LukasKropf/nadia-hardware/housing/Explosion.png

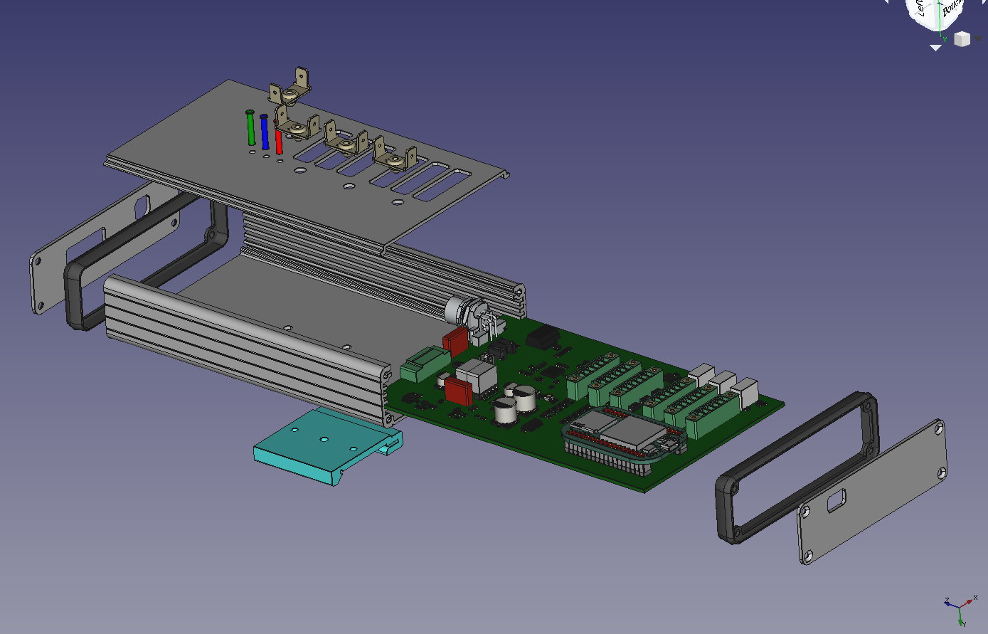
housing/Explosion.png
