LukasKropf/nadia-hardware/housing/Explosion_transparten_Beschriftet.png

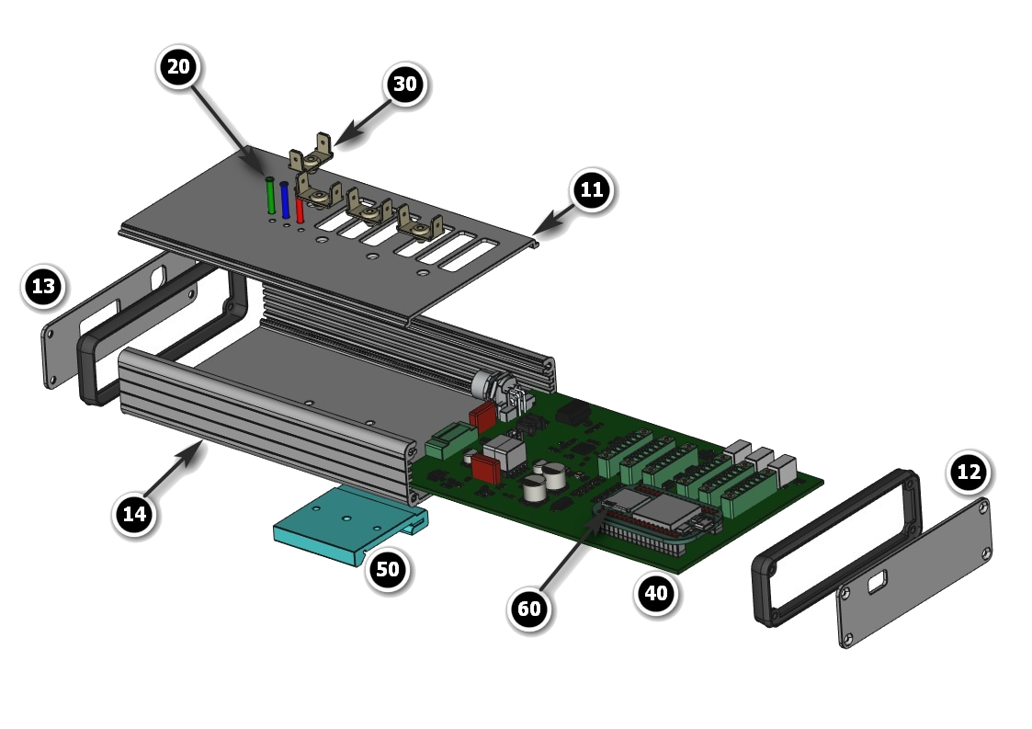
housing/Explosion_transparten_Beschriftet.png
