LukasKropf/nadia-hardware/housing/Explosion_weiss.jpg

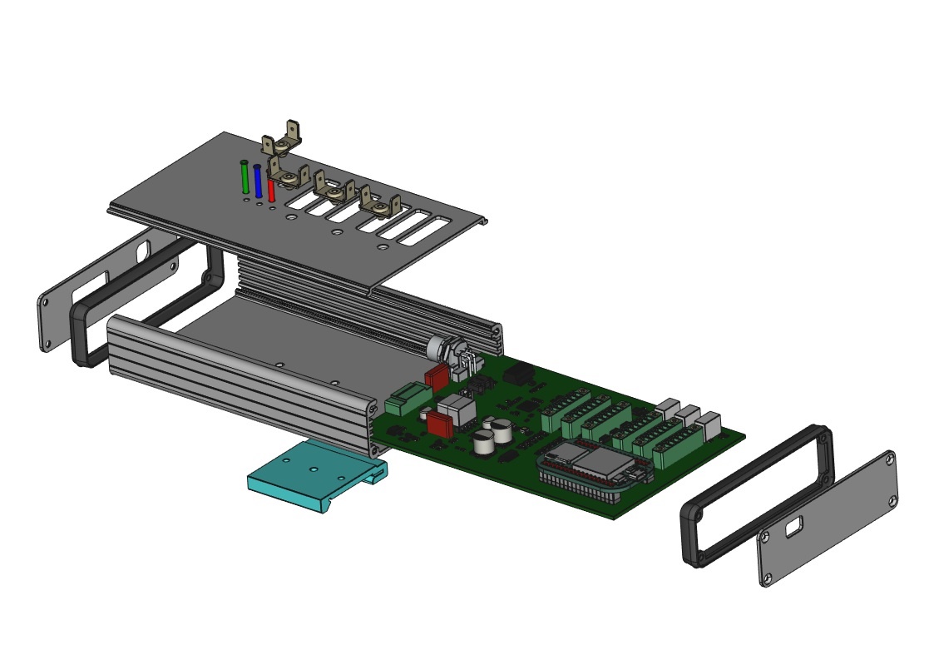
housing/Explosion_weiss.jpg
