LukasKropf/nadia-hardware/PCB/Simulationen/2018-10-04_212918_LUKAS-PC.png

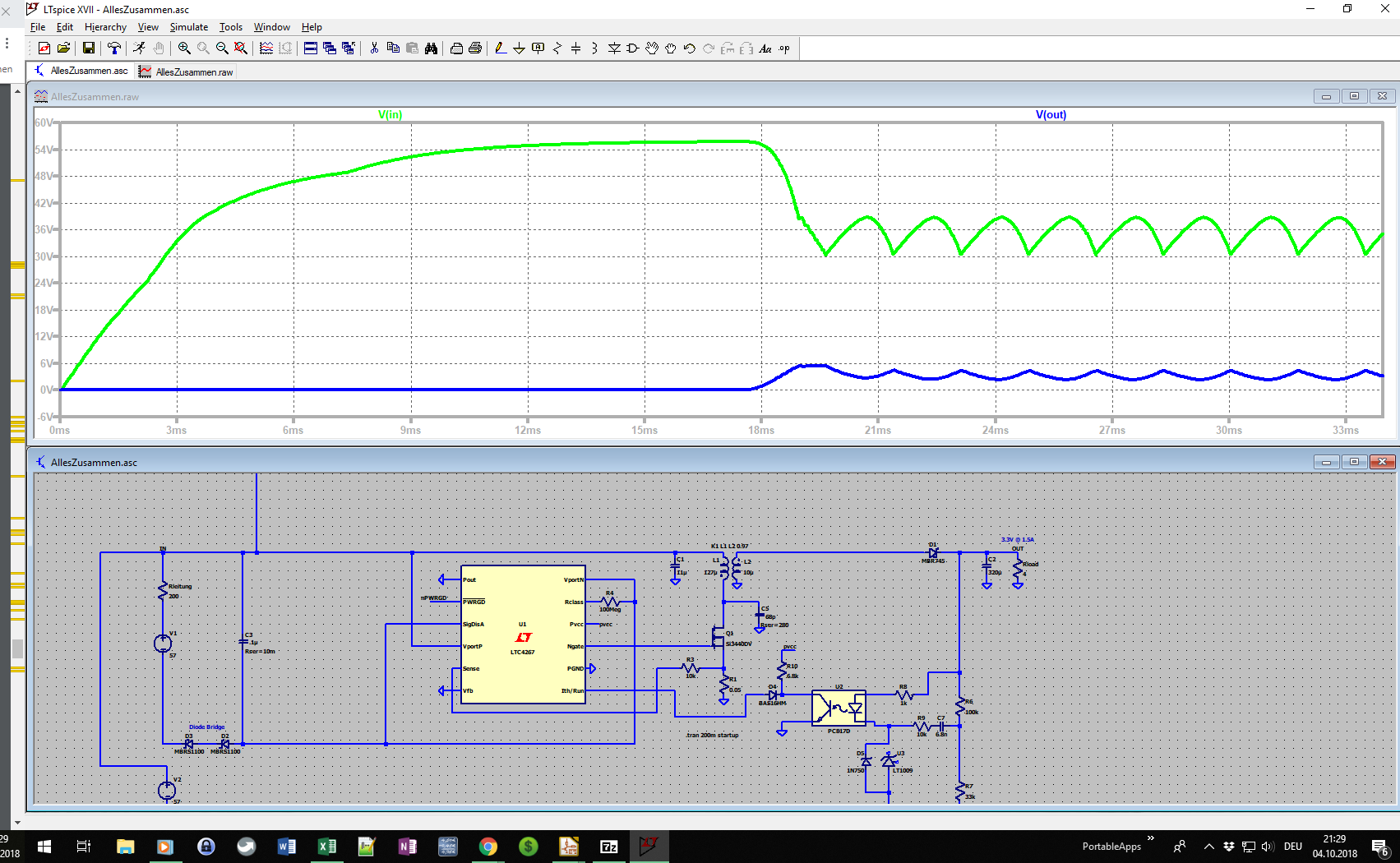
PCB/Simulationen/2018-10-04_212918_LUKAS-PC.png
