LukasKropf/nadia-hardware/PCB/Simulationen/AllesZusammen.asc

C1: cap; 11µ; Rser=100m
C2: cap; 320µ; Rser=10m
C3: cap; .1µ; Rser=10m
C4: cap; 10µ
C5: cap; 68p; Rser=280
C7: cap; 6.8n
C9: cap; 47n
D1: schottky; MBR745
D2: schottky; MBRS1100
D3: schottky; MBRS1100
D4: diode; BAS16HM
D5: zener; 1N750
D7: zener; BZX84C9V1L
L1: ind2; 127µ; Rser=0.1
L2: ind2; 10µ; Rser=10m
Q1: nmos; Si3440DV
Q4: npn; 2N3019
R1: res; 0.05
R3: res; 10k
R4: res; 100Meg
R6: res; 100k
R7: res; 33k
R8: res; 1k
R9: res; 10k
R10: res; 6.8k
R16: res; 220k
R17: res; 220k
R19: res; 100
Rleitung: res; 0
Rload: res; 4
U1: LTC4267
U2: PC817D
V1: voltage; PULSE(0 40 0 100m)
Named nets: 0, OUT, IN, pvcc, nPWRGD, pout
.tran 200m startup
K1 L1 L2 0.97
Diode Bridge
3.3V @ 1.5A
