LukasKropf/nadia-hardware/PCB/Simulationen/AnalogEingang.asc

C1: cap; 47n
D2: zener; TDZ24B
R1: res; 560k
R3: res; 560k
R4: res; 47k
R5: res; 10
R6: res; 10
Rmessung: res; 1Meg
V1: voltage; 50; AC 1
V2: voltage; PULSE(0 15000 0.8 10n 10n 100u 150u 10)
V3: voltage; PULSE(0 -15k 0.75 10n 10n 50u 150u 10)
Named nets: 0, out, in, V24
.dc V1 -100 +100 0.1
;tran 0 2 0
;ac dec 20 0.1 10meg
