LukasKropf/nadia-hardware/PCB/Simulationen/DigitalEingang.asc

A1: schmtbuf; Vt=1.8 Vh=0.06
C1: cap; 47n
D1: schottky; 1N5817
D2: schottky; 1N5817
R1: res; 560k
R2: res; 560k
R3: res; 1k
R4: res; 10k
Rmessung: res; 1Meg
V1: voltage; PULSE(0 50 0 1 1 0 2)
V3: voltage; 3.3
Named nets: 0, out, in, 3V3
.dc V1 -100 +100 0.1
;tran 0 5 0
;ac dec 50 1 1meg
