LukasKropf/nadia-hardware/PCB/Simulationen/Draft1.asc

D1: zener; KDZ11B
M1: nmos; IPD122N10N3
R1: res; 100k
R2: res; 10
V1: voltage; ""
Named nets: 0
;op
.dc V1 -50 50 0.1
