LukasKropf/nadia-hardware/PCB/Simulationen/EinAusschaltLogik.asc

C310: cap; 47n
C320: cap; 47n
C321pvcc: cap; 10µ
D310: diode; MURS120
D320: diode; MURS120
D321: zener; BZX84B9V1L
M1: nmos; BUK9219-55A
Q310: npn; 2N3019
Q320: npn; 2N3019
R5: res; 4.5k
R8: res; 30
R310: res; 220k
R311: res; 10k
R312: res; 100
R320: res; 220k
R321: res; 100
R322start: res; 220k
S1: sw; MySW
V1: voltage; {x}
V2: voltage; PULSE(10 10 0.5 0.001 0.001 0.5 1)
V3: voltage; PULSE(0 10 0 0.1n 0.1n 20n 5u)
Named nets: 0, pvcc, nPWRGD, VportP, Rlast
.tran 0 0.2 0.1
.meas EnergyQ1 INTEG Ic(Q1) FROM 0 TO 1.5
LTC4267 nPWRGD Signal Simulation.
.step param x list 36 48 57
.model MYSW SW(Ron=1n Roff=100Meg Vt=5 Vh=-1)
.meas Prms RMS I(V1)*V(vportp) FROM 0 TO 0.1
