LukasKropf/nadia-hardware/PCB/Simulationen/EinAusschaltLogikAlternativ.asc

C1: cap; 10µ
C2: cap; 47n
D1: zener; BZX84B9V1L
D3: diode; MURS120
M1: nmos; BUK9219-55A
Q1: npn; 2N3019
R1: res; 220k
R2: res; 10k
R3: res; 100gig
R4: res; 7.2k
R5: res; 4.5k
R8: res; 30
S1: sw; MySW
V1: voltage; {x}
V2: voltage; PULSE(10 10 0.5 0.001 0.001 0.5 1)
V3: voltage; PULSE(0 10 0 0.1n 0.1n 20n 5u)
Named nets: 0, pvcc, nPWRGD, VportP, Rlast
.tran 0 0.2 0.1
.meas EnergyQ1 INTEG Ic(Q1) FROM 0 TO 1.5
LTC4267 nPWRGD Signal Simulation.
.step param x list 36 48 57
.model MYSW SW(Ron=1n Roff=100Meg Vt=5 Vh=-1)
.meas Prms RMS I(V1)*V(vportp) FROM 0 TO 0.1
