LukasKropf/nadia-hardware/PCB/Simulationen/EingangMItFerriteBead.asc

C1: cap; 100p
C2: cap; 100p
C3: cap; 10n
L1: FerriteBead; 3.7µ; Ipk=1 Rser=0.179 Rpar=1100 Cpar=1.15p mfg="Würth Elektronik" pn="782763102 WE-CBA 1206"
R1: res; 5k
R2: res; 50
R3: res; 0.05
V1: voltage; PULSE(-10 10 0 1u 1u 3.3e-5 6.6e-5); Rser=2k
V2: voltage; PULSE(0 2000 0 5n 20n 25n 6.6e-6 150)
Named nets: 0, p, m
.tran 0.01
