LukasKropf/nadia-hardware/PCB/Simulationen/EnableDcDc.asc

M1: nmos; AP9465GEM
R1: res; 50
R2: res; 100k
V1: voltage; 5
V2: voltage; PULSE(0 3.3 0.1)
Named nets: 0
.tran 0.2
