LukasKropf/nadia-hardware/PCB/Simulationen/feedback.asc

C1: cap; 6.8n
R1: res; 100k
R2: res; {x}
R3: res; 1k
R4: res; 0
U1: LT1009
U2: PC817A
V1: voltage; PULSE(0 10 0 10)
V2: voltage; 8
Named nets: 0
.tran 10
.step param x list 33k 66.4k 100k 1000meg
