LukasKropf/nadia-hardware/PCB/Simulationen/Spannungsdrop.asc

C1: polcap; 10000µ; V=6.3 Irms=2.75 Rser=0.02 Lser=0 mfg="Nichicon" pn="UPL0J103MRH" type="Al electrolytic"
C2: polcap; 330µ; V=2.5 Irms=3.87298 Rser=0.015 Lser=0 mfg="KEMET" pn="A700X337M2R5ATE015" type="Al electrolytic"
C3: cap; 33µ; V=6.3 Irms=15.2 Rser=0.00332739 Lser=0 mfg="KEMET" pn="C1210C336K9RAC" type="X7R"
C4: polcap; 330µ; V=2.5 Irms=3.87298 Rser=0.015 Lser=0 mfg="KEMET" pn="A700X337M2R5ATE015" type="Al electrolytic"
C5: polcap; 10000µ; V=6.3 Irms=2.75 Rser=0.02 Lser=0 mfg="Nichicon" pn="UPL0J103MRH" type="Al electrolytic"
C6: polcap; 10000µ; V=6.3 Irms=2.75 Rser=0.02 Lser=0 mfg="Nichicon" pn="UPL0J103MRH" type="Al electrolytic"
D1: diode
R1: res; 8
V1: voltage; PULSE(6 0 1.9 0.1m 0.1m 0.05 2); Rser=0.2
Named nets: 0
.tran 5
UUG0J103MNQ1MS
